septentrio-gnss/moTi/pictures/connections - Copy.png

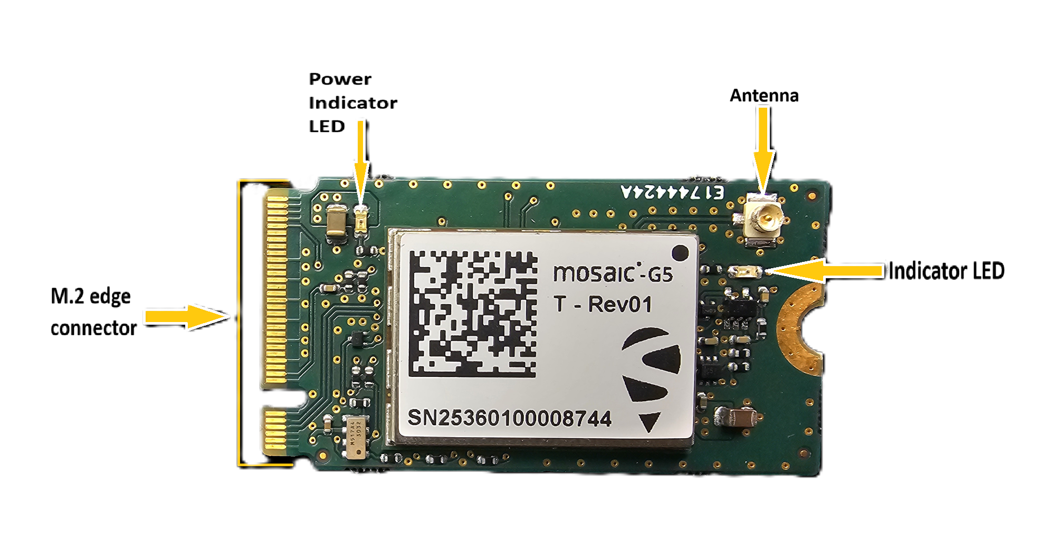
pictures/connections - Copy.png
